IacoT1/ECoS-19/assembly/assembly11.png

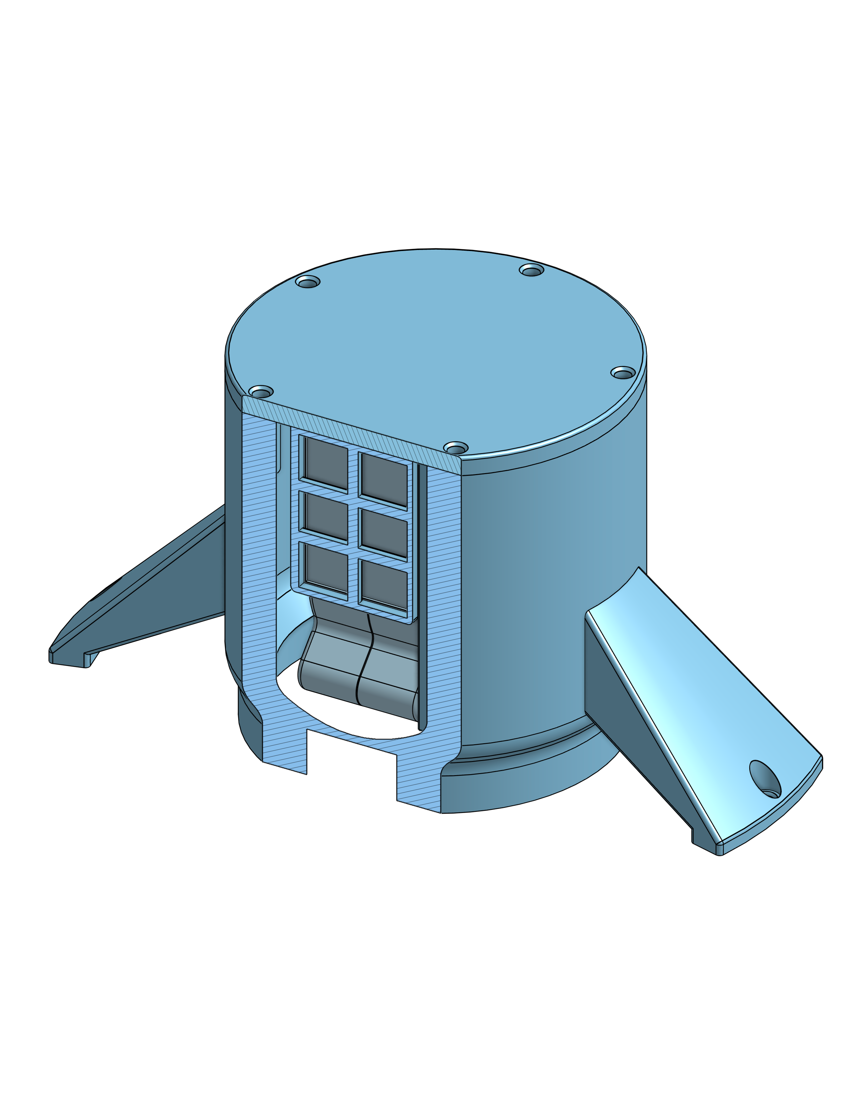
assembly/assembly11.png
